girishsarwal/gt-jtx/gt-jtx-m8/build-photos/IMAG0157.jpg

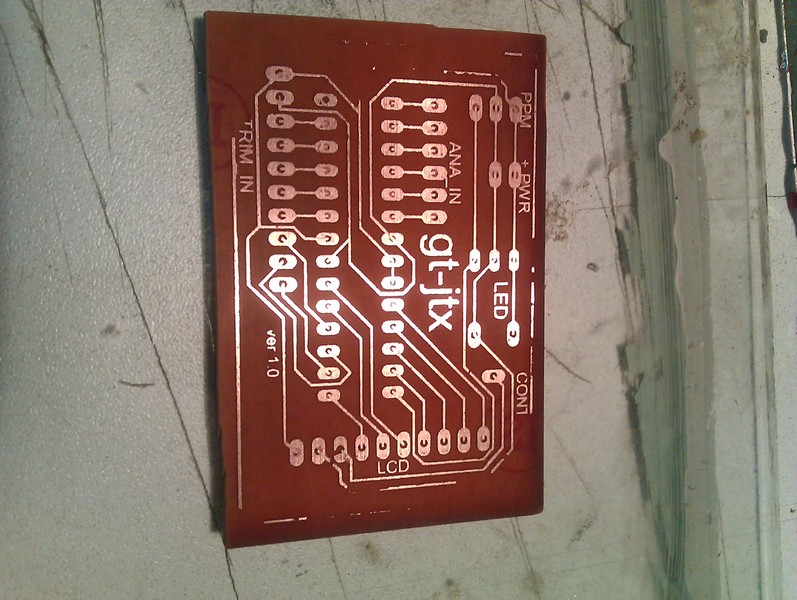
gt-jtx-m8/build-photos/IMAG0157.jpg
