girishsarwal/gt-jtx/gt-jtx-m8/build-photos/IMAG0159.jpg

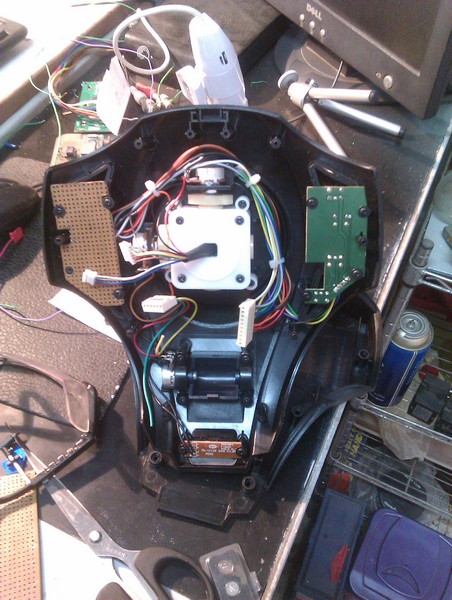
gt-jtx-m8/build-photos/IMAG0159.jpg
