girishsarwal/gt-jtx/gt-jtx-m8/build-photos/IMAG0160.jpg

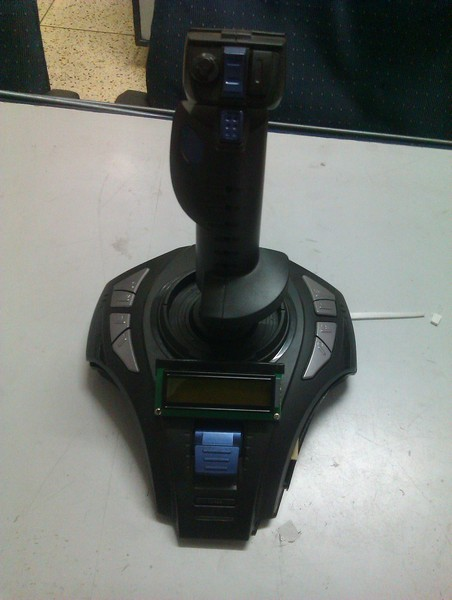
gt-jtx-m8/build-photos/IMAG0160.jpg
