girishsarwal/gt-jtx/gt-jtx-m8/build-photos/IMAG0162.jpg

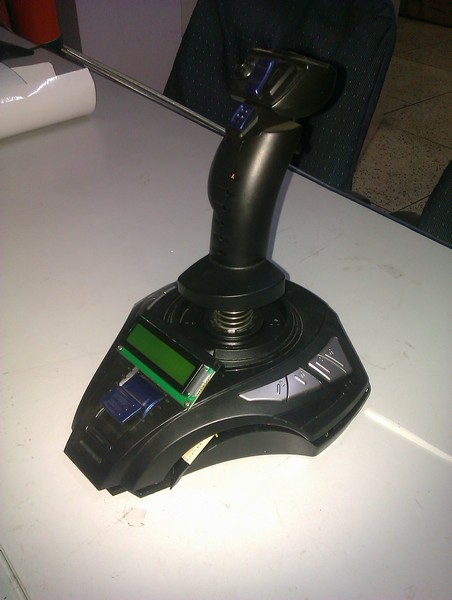
gt-jtx-m8/build-photos/IMAG0162.jpg
