girishsarwal/gt-jtx/gt-jtx-m8/build-photos/IMG_1432.JPG

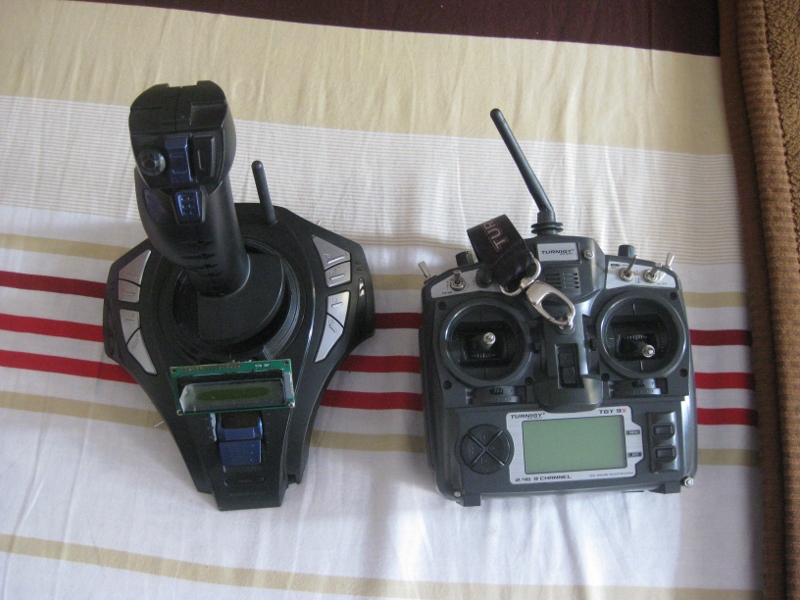
gt-jtx-m8/build-photos/IMG_1432.JPG
