girishsarwal/gt-jtx/gt-jtx-m8/build-photos/IMG_1434.JPG

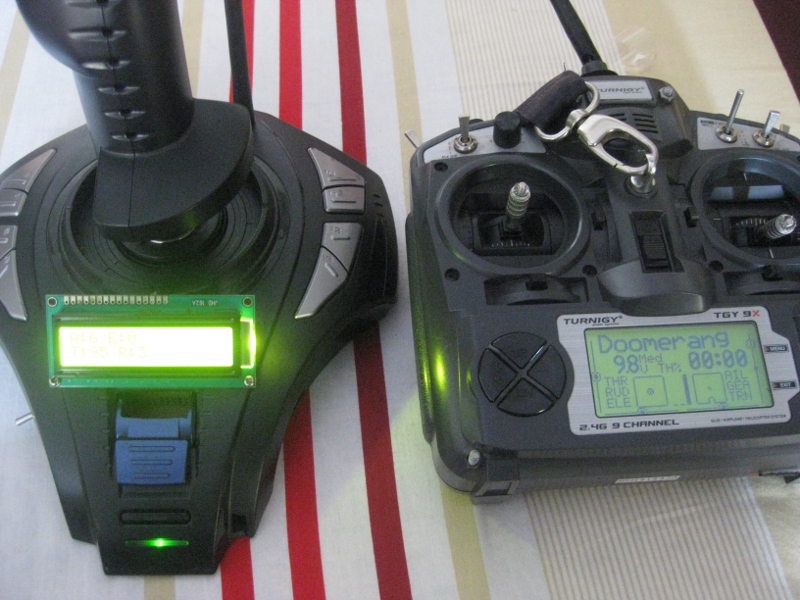
gt-jtx-m8/build-photos/IMG_1434.JPG
