girishsarwal/gt-jtx/gt-jtx-m8/build-photos/IMG_1441.JPG

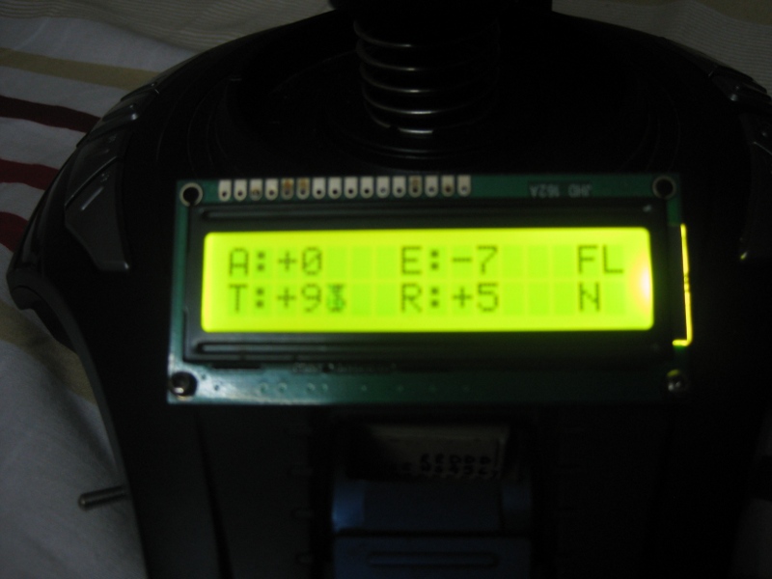
gt-jtx-m8/build-photos/IMG_1441.JPG
